shannon-greenlight/PBJ_New/spice/newmon.asc

D1: LED
D2: LED
R11: res; 1K
U1: AD711
V1: voltage; 12
V4: voltage; 12
V5: signal; SINE(0 5 2 0 0); AC 1
Named nets: 0
.tran 0 2 1 .1
