shannon-greenlight/PBJ_New/spice/sigmon2.asc

D1: LED
D2: zener; 1N750
D3: LED
D4: zener; 1N750
R1: res; 2.2K
R2: res; 470
R4: res; 1K
R5: res; 10K
R9: res; 10K
R11: res; 100K
R13: res; 330K
U1: AD711
V1: voltage; 12
V4: voltage; 12
V5: signal; SINE(0 .25 2 0 0); AC 1
Named nets: 0
.tran 0 2 1 .1
