shannon-greenlight/PBJ_New/spice/sigmon.asc

D1: LED
D2: LED
R1: res; 1K
R2: res; 1K
R3: res; 200K
R4: res; 91K
R5: res; 20K
R6: res; 20K
R11: res; 100K
R13: res; 330K
U1: AD711
U2: AD711
V1: voltage; 12
V4: voltage; 12
V5: signal; SINE(0 .3 2 0 0); AC 1
Named nets: 0
.tran 0 2 1 .1
